sanni/cartreader/hardware/cic_adapter/D411_F411_adapter.jpg

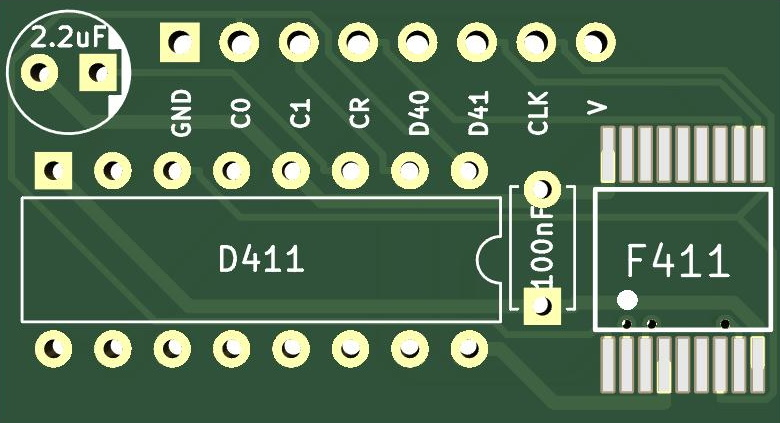
hardware/cic_adapter/D411_F411_adapter.jpg
