sanni/cartreader/hardware/cic_adapter/PIC_adapter_schematics.jpg

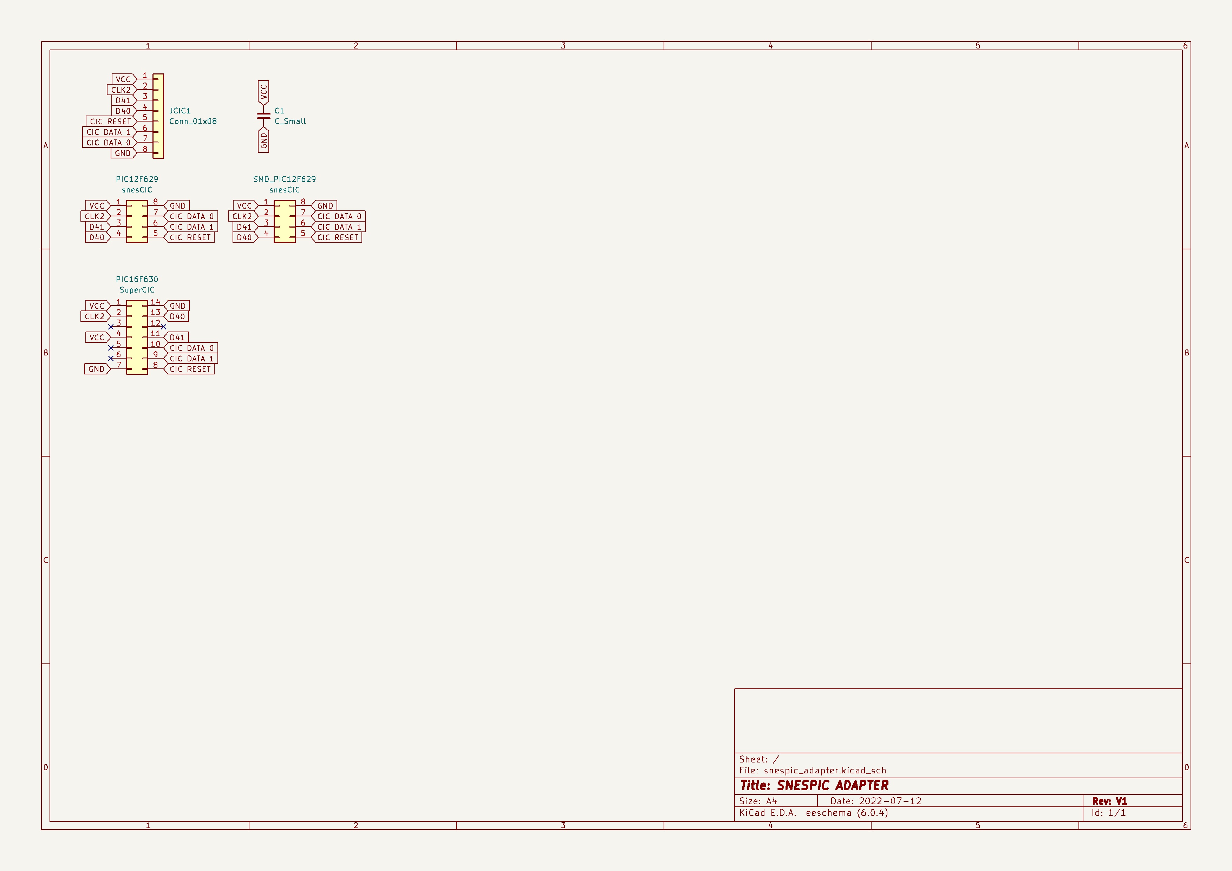
hardware/cic_adapter/PIC_adapter_schematics.jpg
