sanni/cartreader/hardware/famicom_adapter/famicom_adapter.jpg

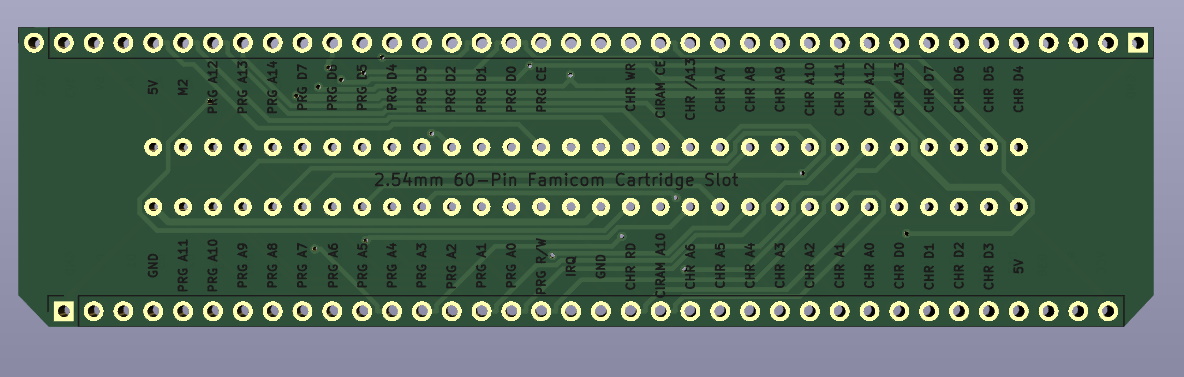
hardware/famicom_adapter/famicom_adapter.jpg
