sanni/cartreader/hardware/famicom_adapter/famicom_adapter_schematics.jpg

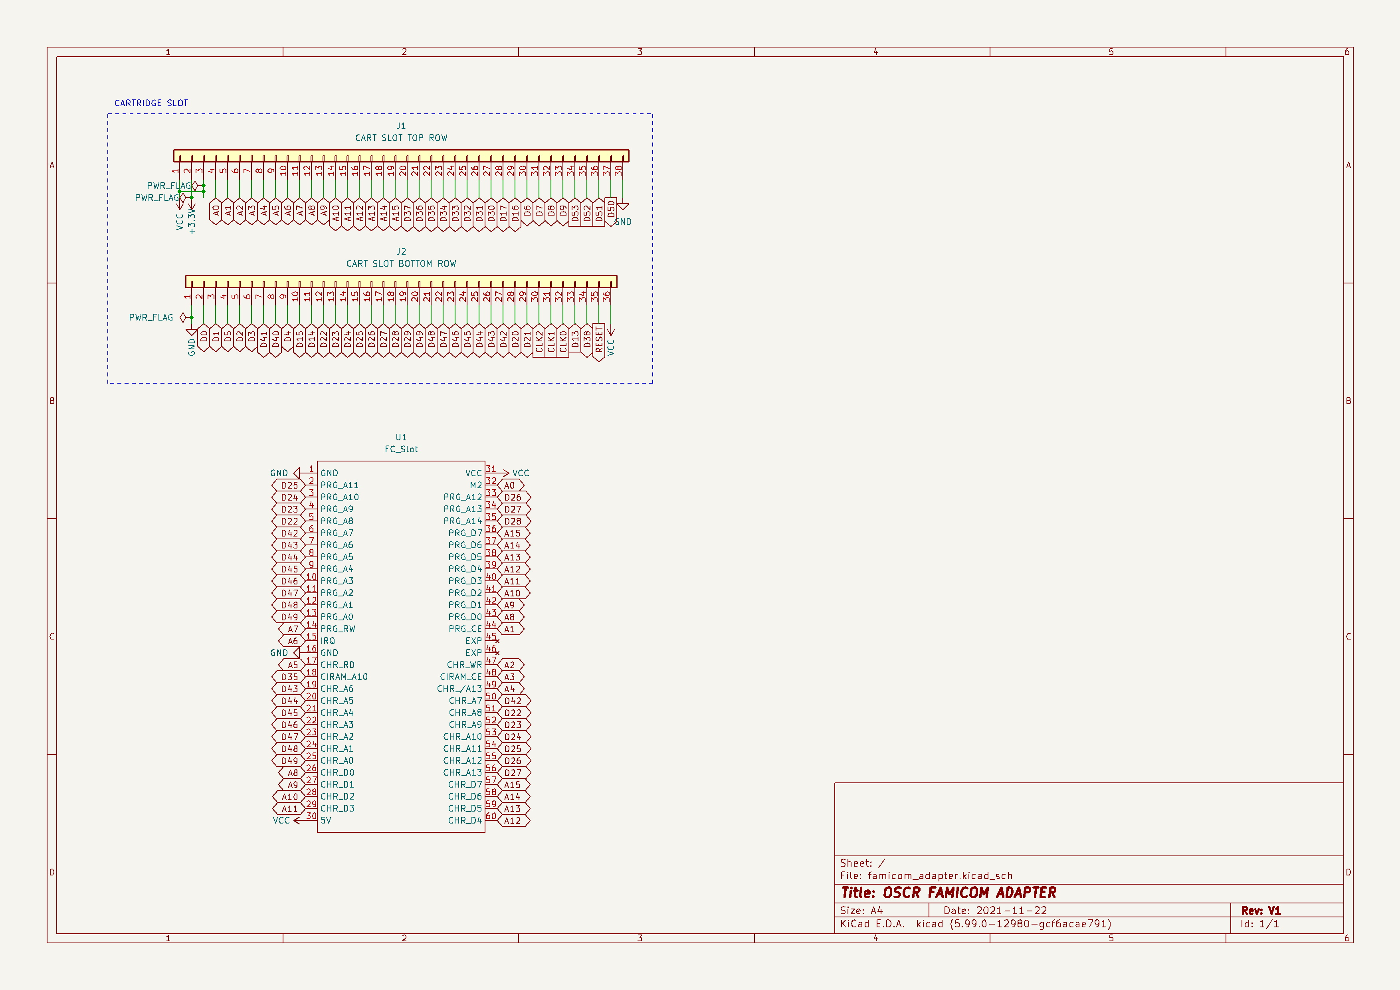
hardware/famicom_adapter/famicom_adapter_schematics.jpg
