sanni/cartreader/hardware/main_pcb_hw5/main_pcb_hw5.jpg

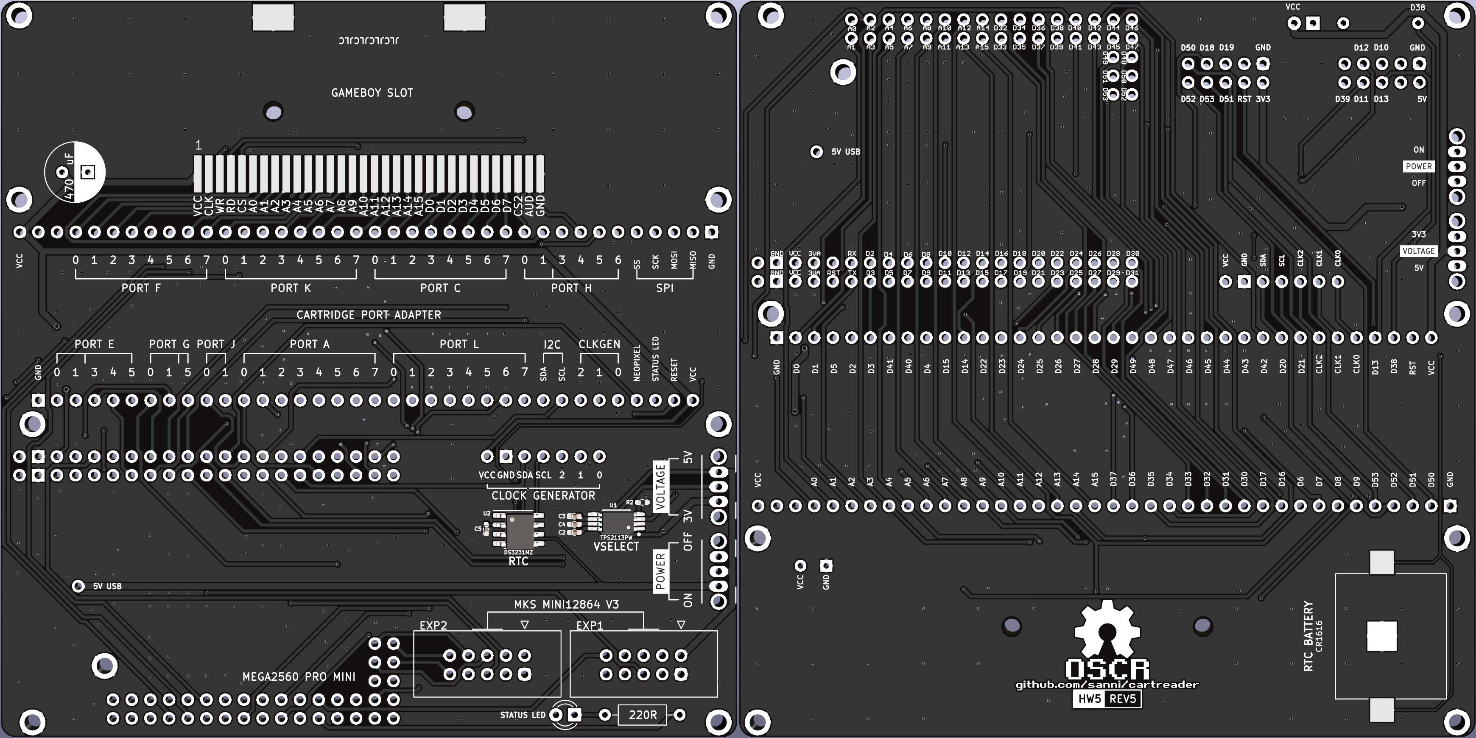
hardware/main_pcb_hw5/main_pcb_hw5.jpg
