sanni/cartreader/hardware/mastersystem_adapter/mastersystem_adapter_schematic.jpg

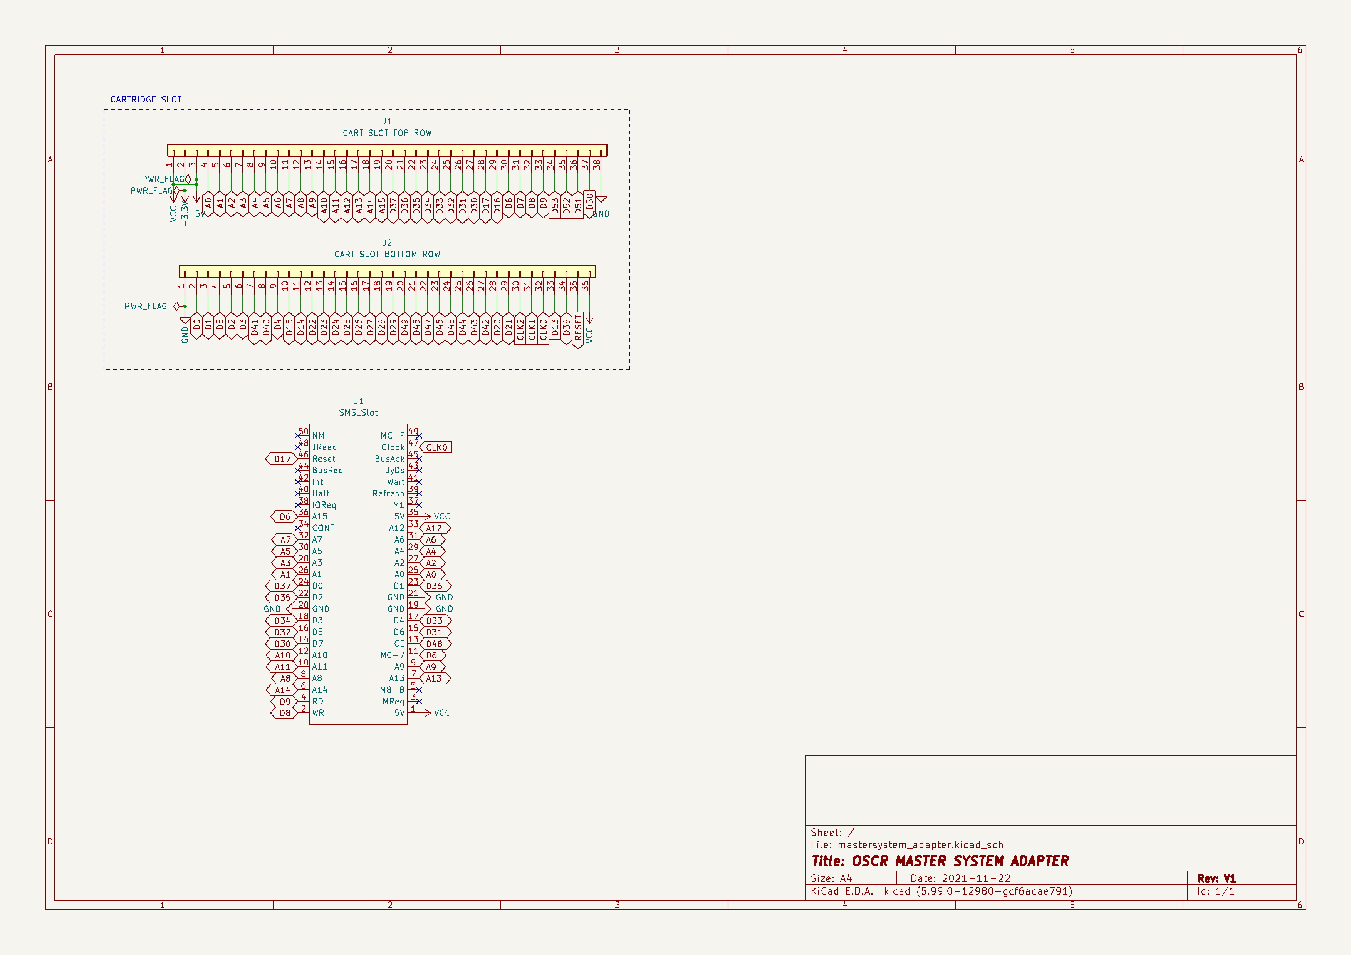
hardware/mastersystem_adapter/mastersystem_adapter_schematic.jpg
