sanni/cartreader/hardware/megadrive_adapter/megadrive_adapter.jpg

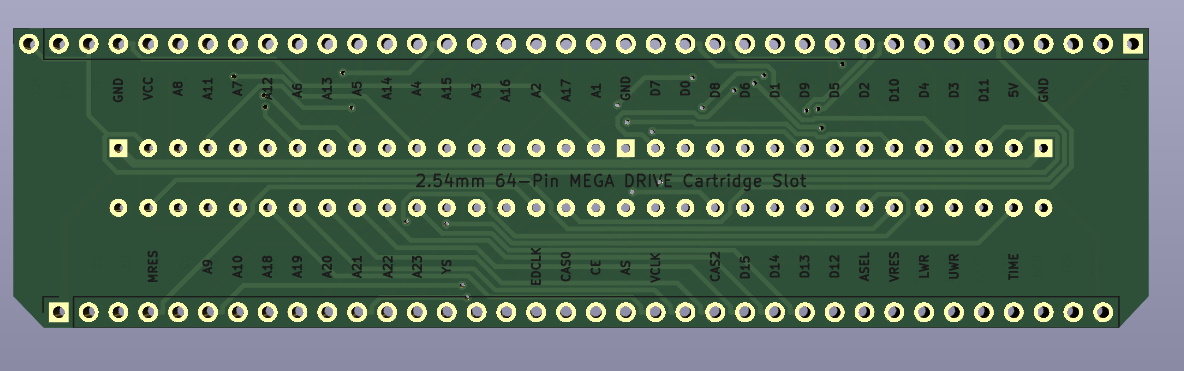
hardware/megadrive_adapter/megadrive_adapter.jpg
