sanni/cartreader/hardware/megadrive_adapter/megadrive_adapter_schematic.jpg

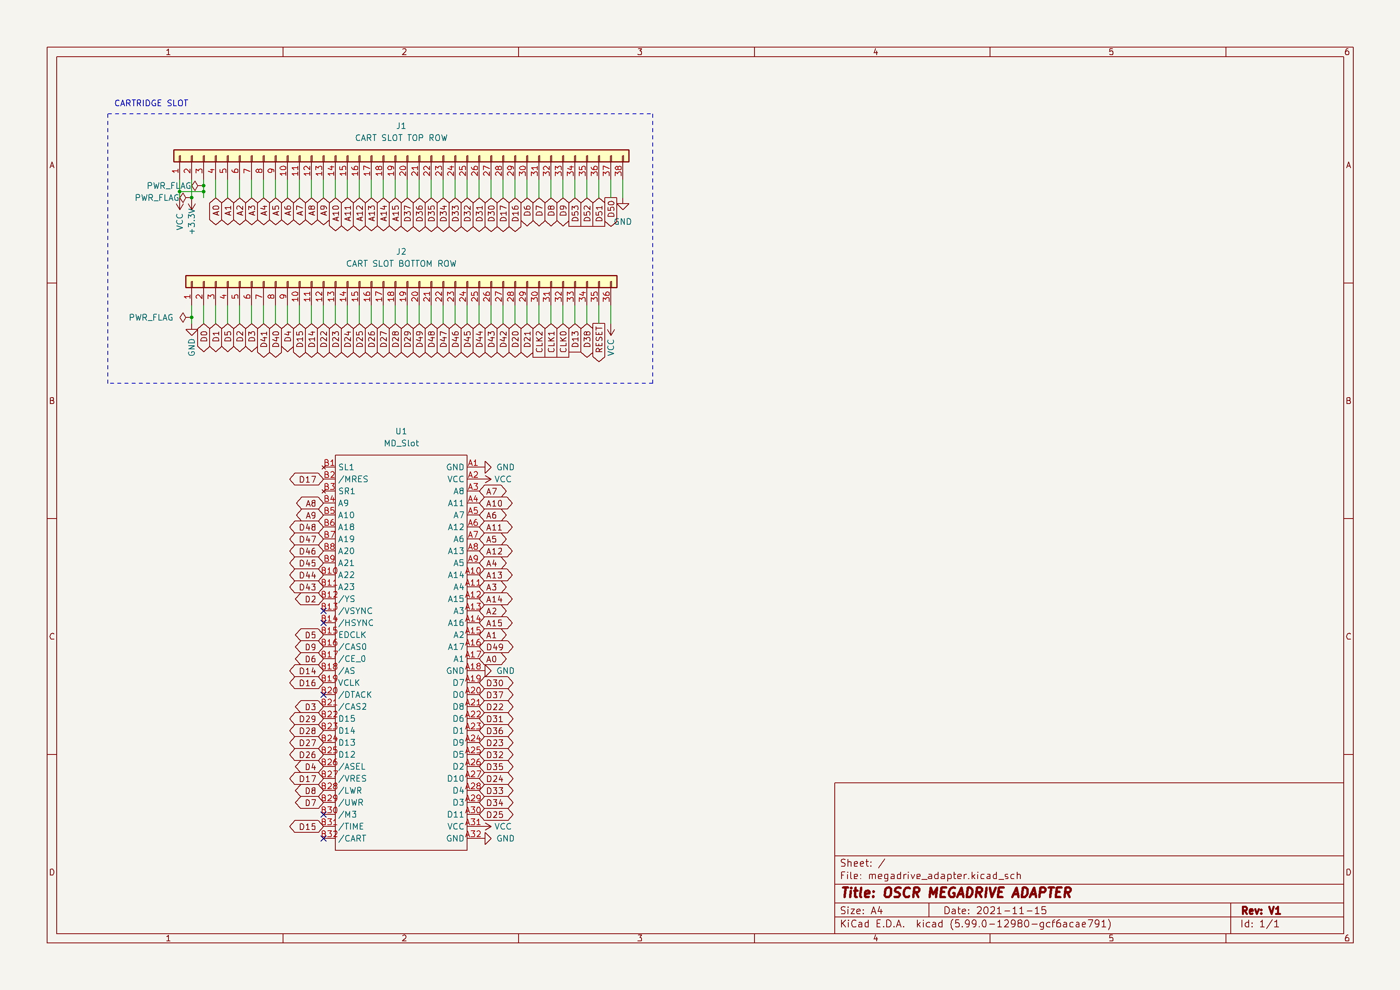
hardware/megadrive_adapter/megadrive_adapter_schematic.jpg
