sanni/cartreader/hardware/n64_adapter/n64_adapter.jpg

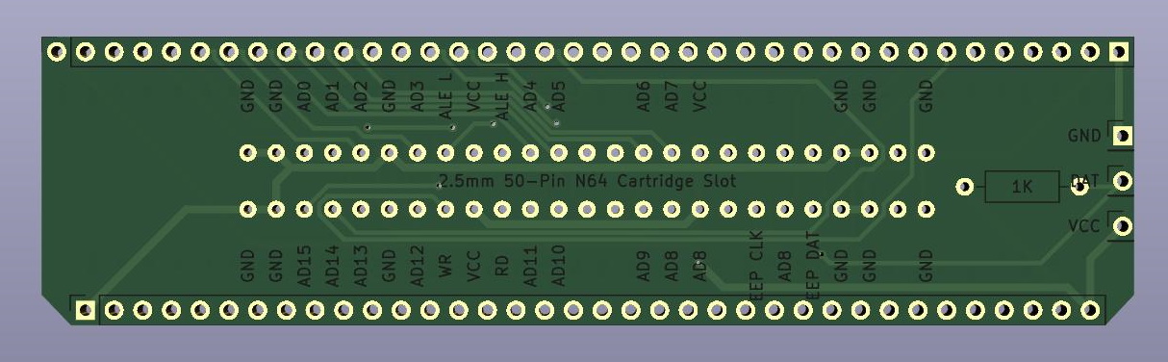
hardware/n64_adapter/n64_adapter.jpg
