sanni/cartreader/hardware/snes_adapter/snes_adapter.jpg

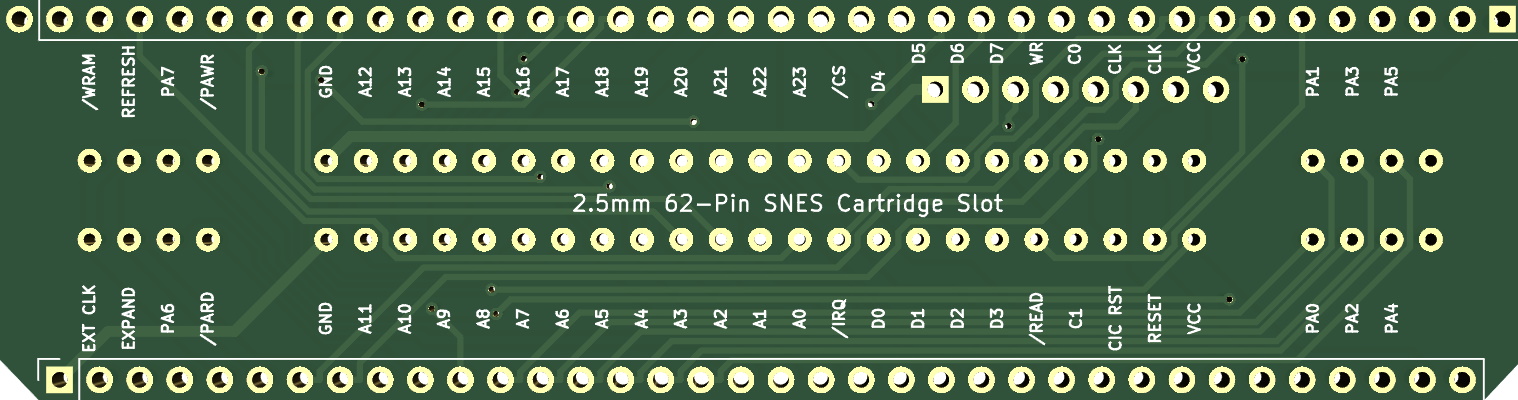
hardware/snes_adapter/snes_adapter.jpg
