sanni/cartreader/hardware/snes_adapter/snes_adapter_schematic.jpg

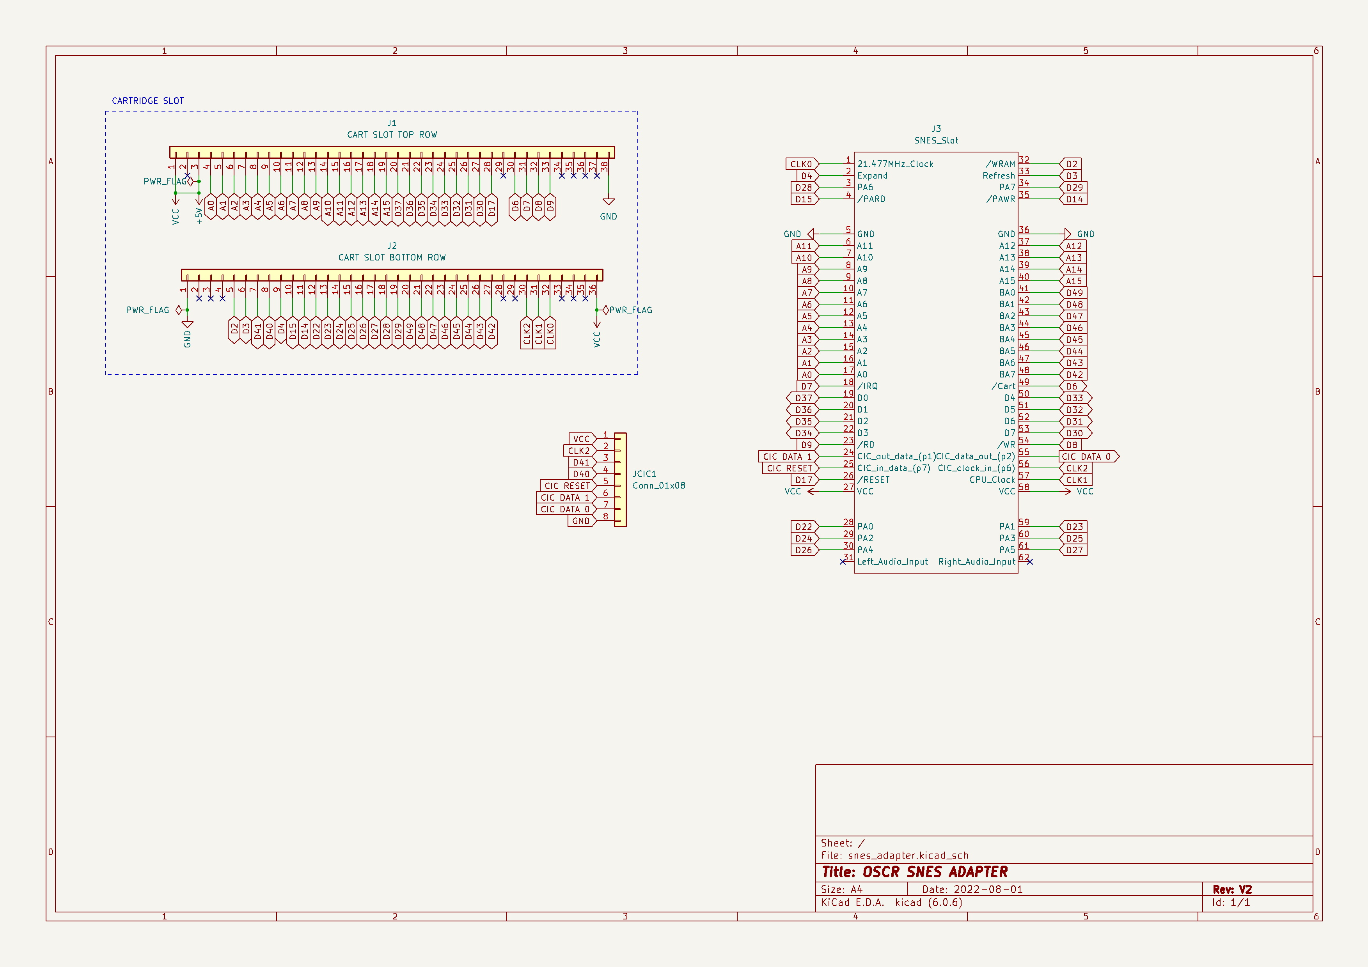
hardware/snes_adapter/snes_adapter_schematic.jpg
