sanni/cartreader/hardware/vselect/VSelect.jpg

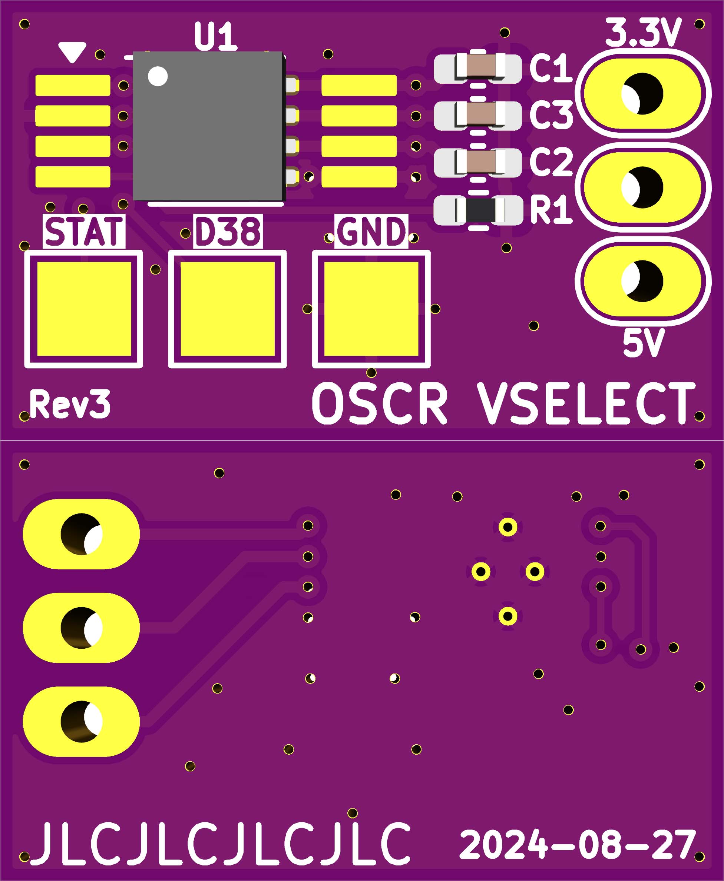
hardware/vselect/VSelect.jpg
