sanni/cartreader/Cart_Reader/GB.ino

//******************************************
// GAME BOY MODULE
//******************************************
#ifdef ENABLE_GBX

/******************************************
   Variables
 *****************************************/
// Game Boy
word sramBanks;
word romBanks;
word lastByte = 0;
boolean audioWE = 0;

/******************************************
   Menu
 *****************************************/
// GBx start menu
static const char gbxMenuItem1[] PROGMEM = "Game Boy (Color)";
static const char gbxMenuItem2[] PROGMEM = "GB Advance (3V)";
static const char gbxMenuItem3[] PROGMEM = "Flash Repro";
static const char gbxMenuItem4[] PROGMEM = "NPower GB Memory";
static const char gbxMenuItem5[] PROGMEM = "Flash Codebreaker";
static const char gbxMenuItem6[] PROGMEM = "Flash Datel Device";
static const char* const menuOptionsGBx[] PROGMEM = { gbxMenuItem1, gbxMenuItem2, gbxMenuItem3, gbxMenuItem4, gbxMenuItem5, gbxMenuItem6, FSTRING_RESET };

// GB menu items
static const char* const menuOptionsGB[] PROGMEM = { FSTRING_READ_ROM, FSTRING_READ_SAVE, FSTRING_WRITE_SAVE, FSTRING_RESET };

#if defined(ENABLE_FLASH)
// GB Flash items
static const char GBFlashItem1[] PROGMEM = "GB 29F/39SF Repro";
static const char GBFlashItem2[] PROGMEM = "GB CFI Repro";
static const char GBFlashItem3[] PROGMEM = "GB CFI and Save";
static const char GBFlashItem4[] PROGMEM = "GB Smart";
static const char GBFlashItem5[] PROGMEM = "GBA Repro (3V)";
static const char GBFlashItem6[] PROGMEM = "GBA 369-in-1 (3V)";
static const char* const menuOptionsGBFlash[] PROGMEM = { GBFlashItem1, GBFlashItem2, GBFlashItem3, GBFlashItem4, GBFlashItem5, GBFlashItem6, FSTRING_RESET };

// 29F MBC selection items
static const char GBFlashMBCItem1[] PROGMEM = "MBC5";
static const char GBFlashMBCItem2[] PROGMEM = "MBC3";
static const char GBFlashMBCItem3[] PROGMEM = "MBC1";
static const char GBFlashMBCItem4[] PROGMEM = "MBC0";
static const char GBFlashMBCItem5[] PROGMEM = "GB Camera";
static const char* const menuOptionsGBFlashMBC[] PROGMEM = { GBFlashMBCItem1, GBFlashMBCItem2, GBFlashMBCItem3, GBFlashMBCItem4, GBFlashMBCItem5, FSTRING_RESET };

// 29F write enable selection items
static const char GBFlashWEItem1[] PROGMEM = "WR";
static const char GBFlashWEItem2[] PROGMEM = "Audio";
static const char* const menuOptionsGBFlashWE[] PROGMEM = { GBFlashWEItem1, GBFlashWEItem2, FSTRING_RESET };

// 29F erase selection items
static const char GBFlashEraseItem1[] PROGMEM = "Yes";
static const char GBFlashEraseItem2[] PROGMEM = "No";
static const char* const menuOptionsGBFlashErase[] PROGMEM = { GBFlashEraseItem1, GBFlashEraseItem2, FSTRING_RESET };

// 29F command set selection items
static const char GBFlashCommandItem1[] PROGMEM = "29F080/16/32/33";
static const char GBFlashCommandItem2[] PROGMEM = "39SF010/20/40";
static const char GBFlashCommandItem3[] PROGMEM = "29F160";
static const char* const menuOptionsGBFlashCommand[] PROGMEM = { GBFlashCommandItem1, GBFlashCommandItem2, GBFlashCommandItem3, FSTRING_RESET };
#endif

// Pelican Codebreaker, Brainboy, and Monster Brain Operation Menu
static const char PelicanRead[] PROGMEM = "Read Device";
static const char PelicanWrite[] PROGMEM = "Write Device";
static const char* const menuOptionsGBPelican[] PROGMEM = { PelicanRead, PelicanWrite };

// Datel Device Operation Menu
static const char MegaMemRead[] PROGMEM = "Read Mega Memory";
static const char MegaMemWrite[] PROGMEM = "Write Mega Memory";
static const char GameSharkRead[] PROGMEM = "Read GBC GameShark";
static const char GameSharkWrite[] PROGMEM = "Write GBC GameShark";
static const char* const menuOptionsGBDatel[] PROGMEM = { MegaMemRead, MegaMemWrite, GameSharkRead, GameSharkWrite };

#if defined(ENABLE_FLASH)
bool gbxFlashCFI() {
  // Flash CFI
  display_Clear();
  display_Update();
  setup_GB();
  mode = CORE_GB;

  // Change working dir to root
  sd.chdir("/");
  // Launch filebrowser
  filePath[0] = '\0';

  fileBrowser(FS(FSTRING_SELECT_FILE));
  display_Clear();
  identifyCFI_GB();
  if (!writeCFI_GB()) {
    display_Clear();
    println_Msg(F("Flashing failed, time out!"));
    // Prints string out of the common strings array either with or without newline
    print_STR(press_button_STR, 1);
    display_Update();
    return false;
  }
  return true;
}
#endif

void feedbackPressAndReset() {
  // Prints string out of the common strings array either with or without newline
  print_STR(press_button_STR, 1);
  display_Update();
  wait();
  resetArduino();
}

// Common code for setting up GB port used by GB carts, Datel,
// Pelican Codebreaker, MonsterBrain
void setup_GBPort() {
  // Set Address Pins to Output
  //A0-A7
  DDRF = 0xFF;
  //A8-A15
  DDRK = 0xFF;

  // Set Control Pins to Output RST(PH0) CLK(PH1) CS(PH3) WR(PH5) RD(PH6)
  DDRH |= (1 << 0) | (1 << 1) | (1 << 3) | (1 << 5) | (1 << 6);
  // Output a high signal on all pins, pins are active low therefore everything is disabled now
  PORTH |= (1 << 3) | (1 << 5) | (1 << 6);
  // Output a low signal on CLK(PH1) to disable writing GB Camera RAM
  // Output a low signal on RST(PH0) to initialize MMC correctly
  PORTH &= ~((1 << 0) | (1 << 1));

  /* FIXME setup_GB sets this up too. Should this also for Datel and others?
    // Set Audio-In(PH4) to Input
    DDRH &= ~(1 << 4);
    // Enable Internal Pullup
    PORTH |= (1 << 4);
  */

  // Set Data Pins (D0-D7) to Input
  DDRC = 0x00;
  // Enable Internal Pullups
  PORTC = 0xFF;
}

// Start menu for both GB and GBA
void gbxMenu() {
  // create menu with title and 5 options to choose from
  unsigned char gbType;
  // Copy menuOptions out of progmem
  convertPgm(menuOptionsGBx, 7);
  gbType = question_box(F("Select Game Boy"), menuOptions, 7, 0);

  // wait for user choice to come back from the question box menu
  switch (gbType) {
    case 0:
      display_Clear();
      display_Update();
      setup_GB();
      mode = CORE_GB;
      break;

    case 1:
      display_Clear();
      display_Update();
      setup_GBA();
      mode = CORE_GBA;
      break;
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
